MSTKMAD/MK2/03.Firmware/XX.MISC/MAIN 731/SW_EDCPSU_731.rtf

Version | Date | Author | Comment
726 | 21/6/21 | DGB | Only 2 memories instead of 4
727 | 21/6/21 | DGB | Only change memory when output is OFF (Outlatch = OFF)
Channel output changes state together with memory.
Commented the Test section of code.
All serial info is removed because is overlapped with ENA and CHANNEL.
Time of displaying ON / OFF is changed from 1800 to 800
CONT ON is changed to OUT1 ON or OUT2 ON
CONT OFF is changed to OUT OFF
Displaying the ON or OFF has changed to accommodate the indication of 1 and 2.
Libraries have been included in the project to make sure that the version is not changed.
GFX library has been modified (write function) to remove the check of the text>longer than the screen size (that makes the text to wrap).
Version of Arduino used for compilation: 1.8.13
728 | 21/6/21 | DGB | Usage of program memory is 88%
Inverted the CH1 and CH2 to allow pin to pin facing in the daughter board
Removed OVC_ALARM
ISENSE MAX Low limit is raised to be closer to the MAX (reduced hysteresis).
729 | 11 OCT 21 | DGB | Time for ISENSE MAX is changed from 1.6s to 2s
730 | 10 marzo 2022 | DGB | Removed the MEMORIES BOX from the display because it is confusing as there is only 2 possible memories.
Implemented on the main branch (725.3 and not in the DUAL so far)!!
731 | 22 marzo 2022 | DGB | NITRO is now more compatible with Cheyenne machines that have brushless motors. The NITRO is split in two phases: 1) warming phase of 65ms at 4V to awake the machine, and 2) NITRO ramp in RC charge fashion from 4 to 12.3V in around 50ms. Finally the voltage goes to encoderPos (target voltage).
