MSTKMAD/MK2/02.Hardware/MK2 PCBs/03.TESTS/PRUEBA MECANICA-EDCPSUr16D/MECH_EDCPSUr16D_USBC/EDCPSU_M2 v1.dxf

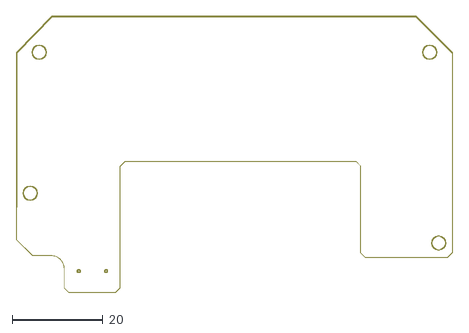
[picture p18: CAD file, 2022-08-05]
02.Hardware/MK2 PCBs/03.TESTS/PRUEBA MECANICA-EDCPSUr16D/MECH_EDCPSUr16D_USBC/EDCPSU_M2 v1.dxf
96.1 x 60.8
