MSTKMAD/MK2/02.Hardware/MK2 PCBs/03.TESTS/USBC-OVC_LIMIT/CAMOutputs/DrawingFiles/USBC-OVC_LIMIT.dxf

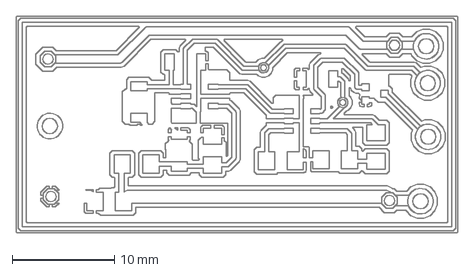
[picture p19: CAD file, 2022-08-05]
02.Hardware/MK2 PCBs/03.TESTS/USBC-OVC_LIMIT/CAMOutputs/DrawingFiles/USBC-OVC_LIMIT.dxf
43.2 x 21.2 mm
