MSTKMAD/MK2/02.Hardware/MK2 PCBs/04.FAJA USBC/FAJA_LARGA_USBC.dxf

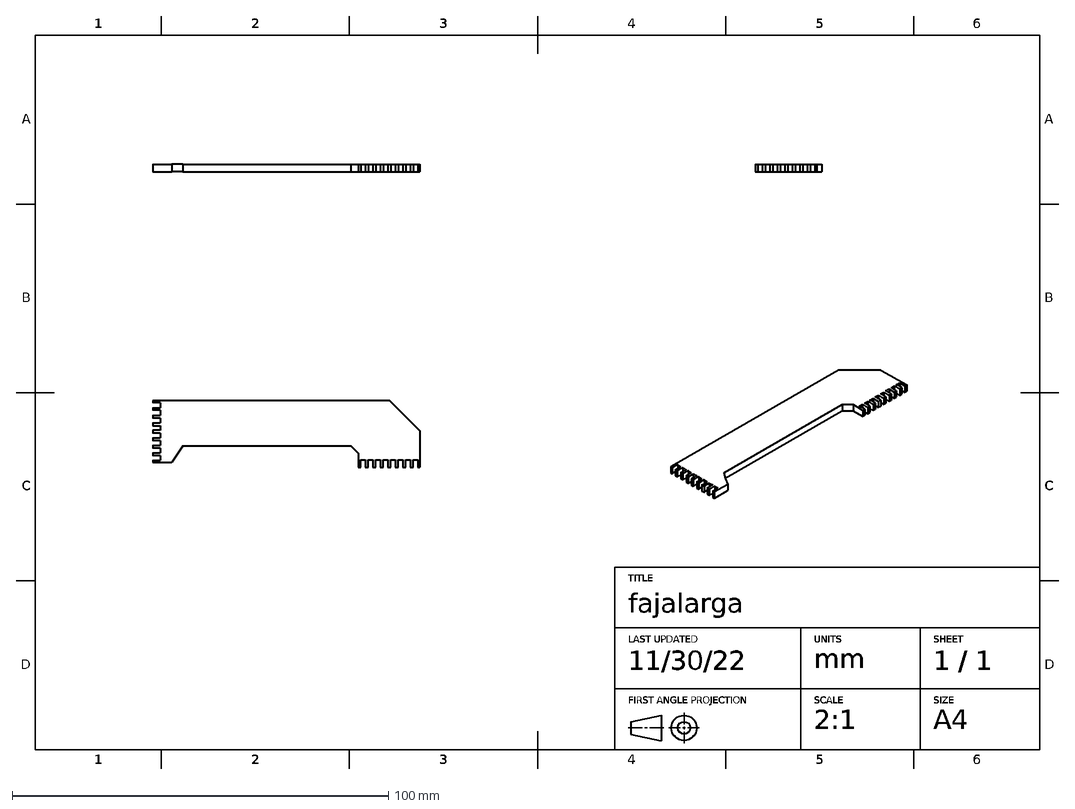
[picture p20: CAD file, 2022-11-30]
02.Hardware/MK2 PCBs/04.FAJA USBC/FAJA_LARGA_USBC.dxf
1
2
3
4
5
6
D
C
B
A
TITLE
fajalarga
LAST UPDATED
11/30/22
UNITS
mm
SHEET
1 / 1
FIRST ANGLE PROJECTION
SCALE
2:1
SIZE
A4
