MSTKMAD/MK2/02.Hardware/MK2 PCBs/02.CONNECTORS/01.Single/FRONT_USBC_1HC_v30.dxf

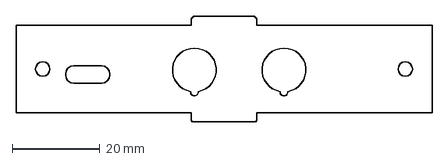
[picture p21: CAD file, 2022-06-15]
02.Hardware/MK2 PCBs/02.CONNECTORS/01.Single/FRONT_USBC_1HC_v30.dxf
95.0 x 24.0 mm
