MSTKMAD/MK2/02.Hardware/MK2 PCBs/03.TESTS/Lentilla/shapr3d_export_2022-05-11_18h31m.dxf

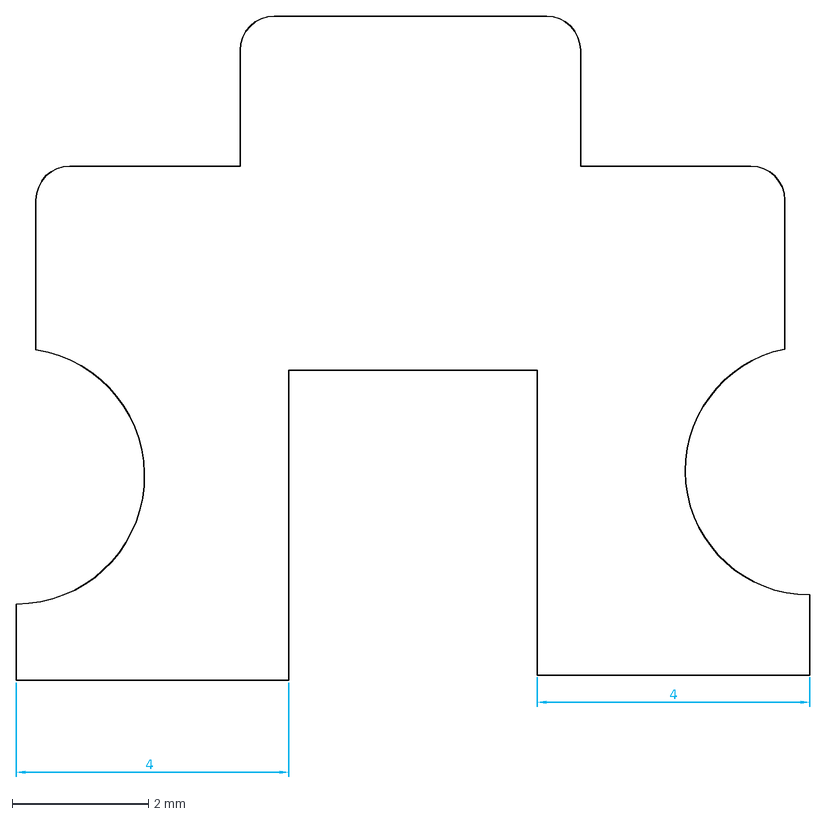
[picture p22: CAD file, 2022-08-05]
02.Hardware/MK2 PCBs/03.TESTS/Lentilla/shapr3d_export_2022-05-11_18h31m.dxf
4
