MSTKMAD/MK2/02.Hardware/MK2 PCBs/04.FAJA USBC/FAJA.dxf

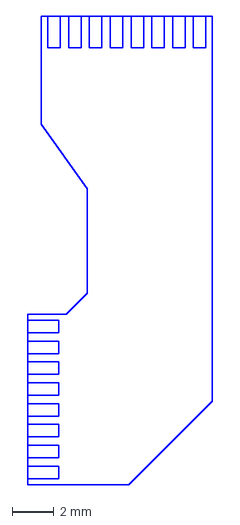
[picture p23: CAD file, 2022-06-13]
02.Hardware/MK2 PCBs/04.FAJA USBC/FAJA.dxf
8.86 x 22.5 mm
