MSTKMAD/MK2/02.Hardware/MK2 PCBs/03.TESTS/Lentilla/shapr3d_export_2022-05-11m.dxf

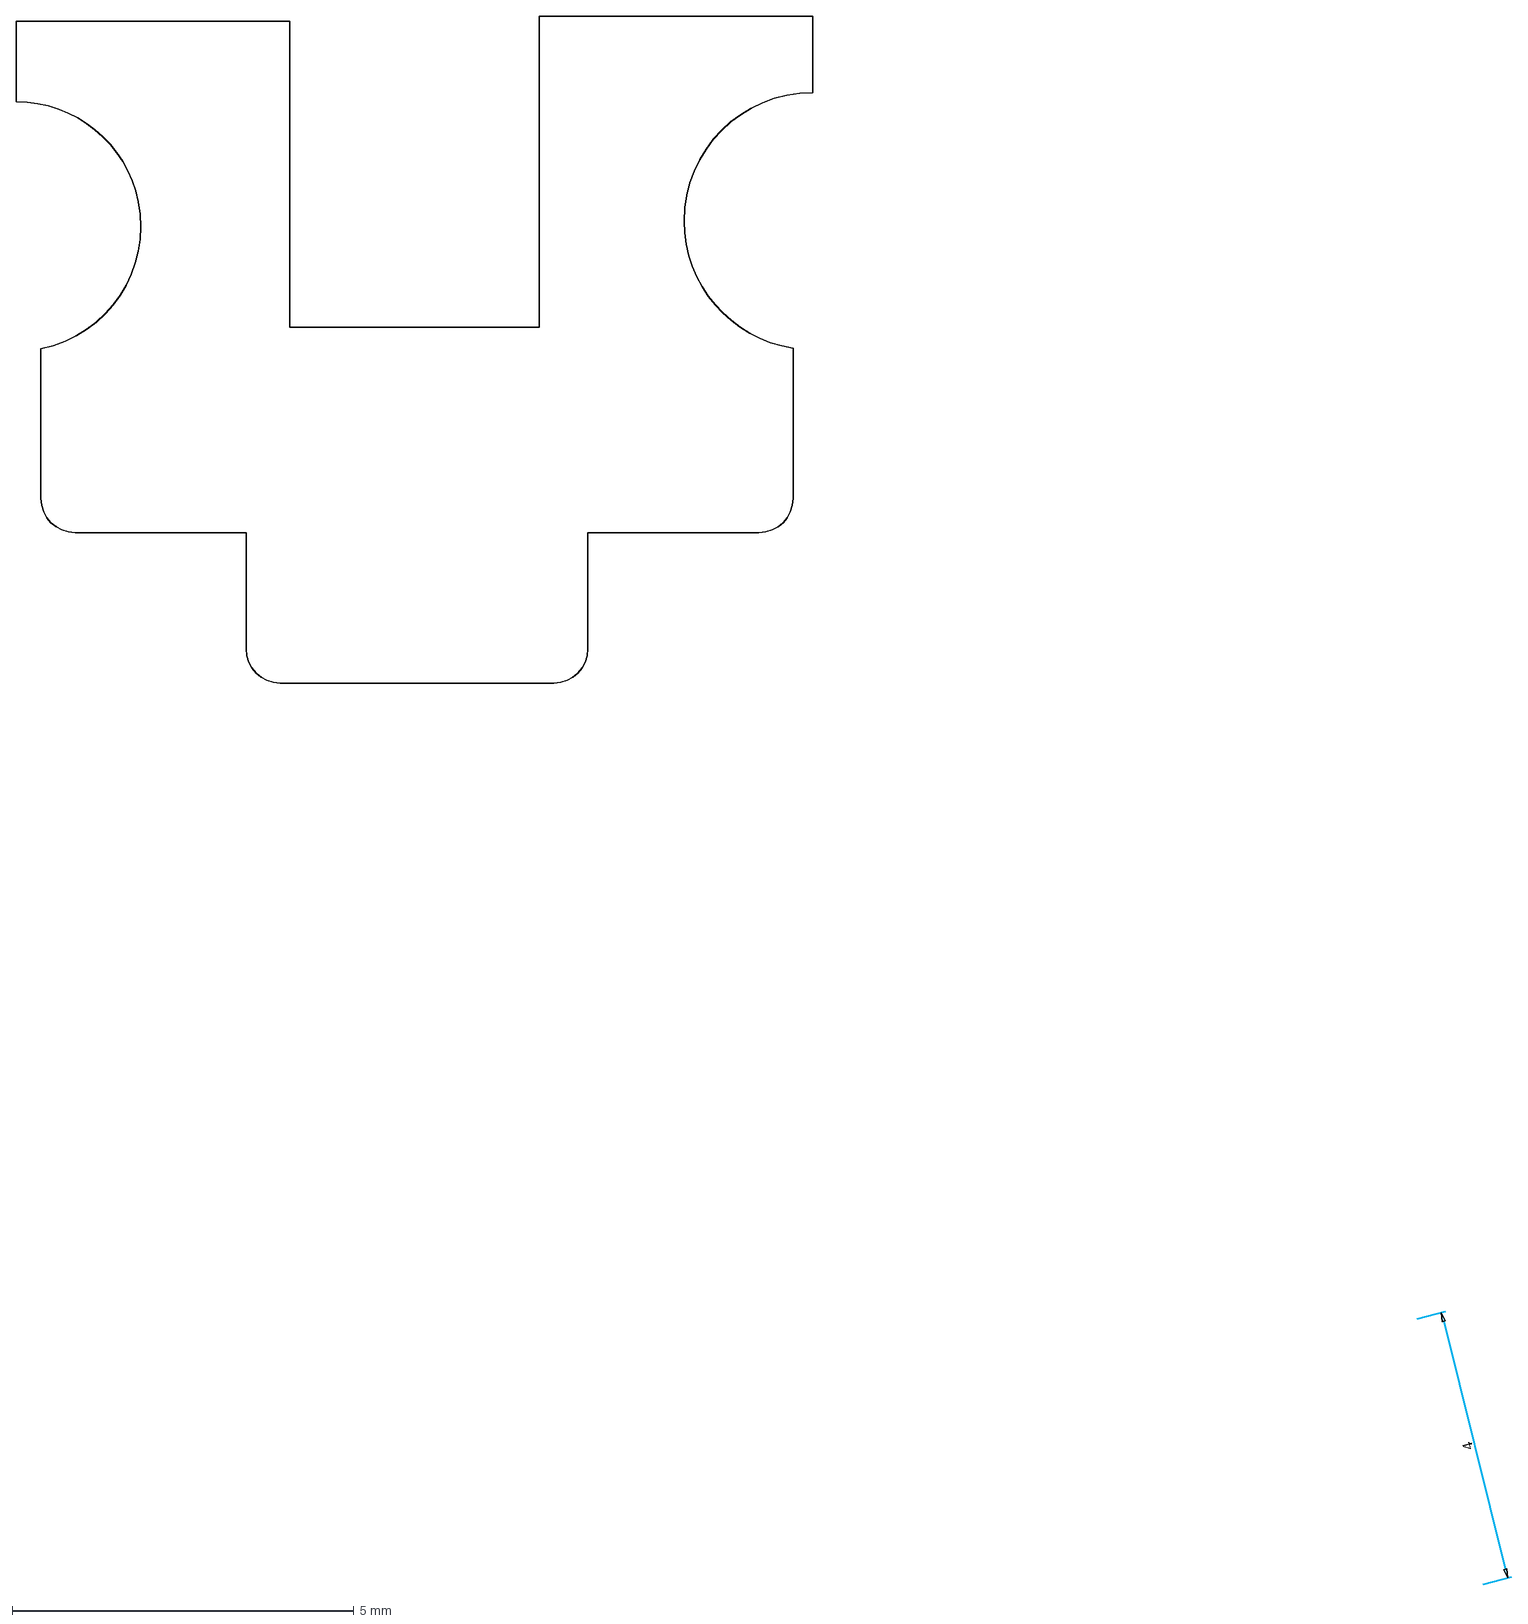
[picture p24: CAD file, 2022-08-05]
02.Hardware/MK2 PCBs/03.TESTS/Lentilla/shapr3d_export_2022-05-11m.dxf
4
