MSTKMAD/MK2/02.Hardware/MK2 PCBs/03.TESTS/PRUEBA MECANICA-EDCPSUr16D/MECH_EDCPSUr16D_USBC/EDCPSU_M2 v1.brd

## EAGLE design 02.Hardware/MK2 PCBs/03.TESTS/PRUEBA MECANICA-EDCPSUr16D/MECH_EDCPSUr16D_USBC/EDCPSU_M2 v1.brd (2022-08-05)

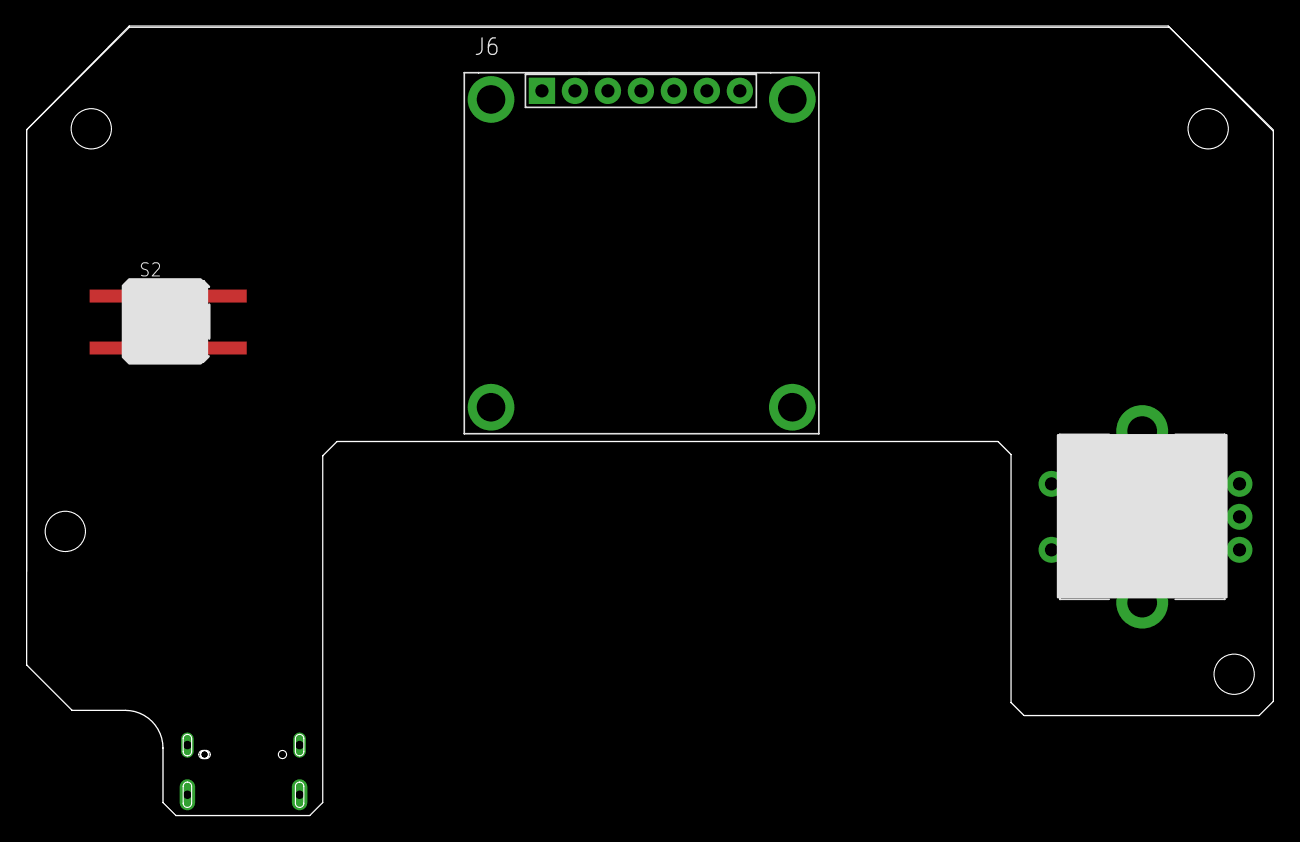
[picture p81: board EDCPSU_M2 v1.brd from above]

Board: 4 copper layers, 96.0 x 60.7 mm, 4 parts (1 on the bottom side), 2 nets, no tracks yet.

Parts:
J4: DX07S016JA1R1500; JAE_DX07S016JA1R1500
J6: Display; OLED_LCD
S1: ROTARTY_ENCODER; ROTARY_ENC_PLAIN
S2: TAC_SW_SMD_KSC931G

Connections:
GND: J4.1, J4.12
VBUS: J4.2, J4.11
