MSTKMAD/MK2/02.Hardware/MK2 PCBs/02.CONNECTORS/00.Dual/Connectors-MK2.brd

## EAGLE design 02.Hardware/MK2 PCBs/02.CONNECTORS/00.Dual/Connectors-MK2.brd (2022-05-24)

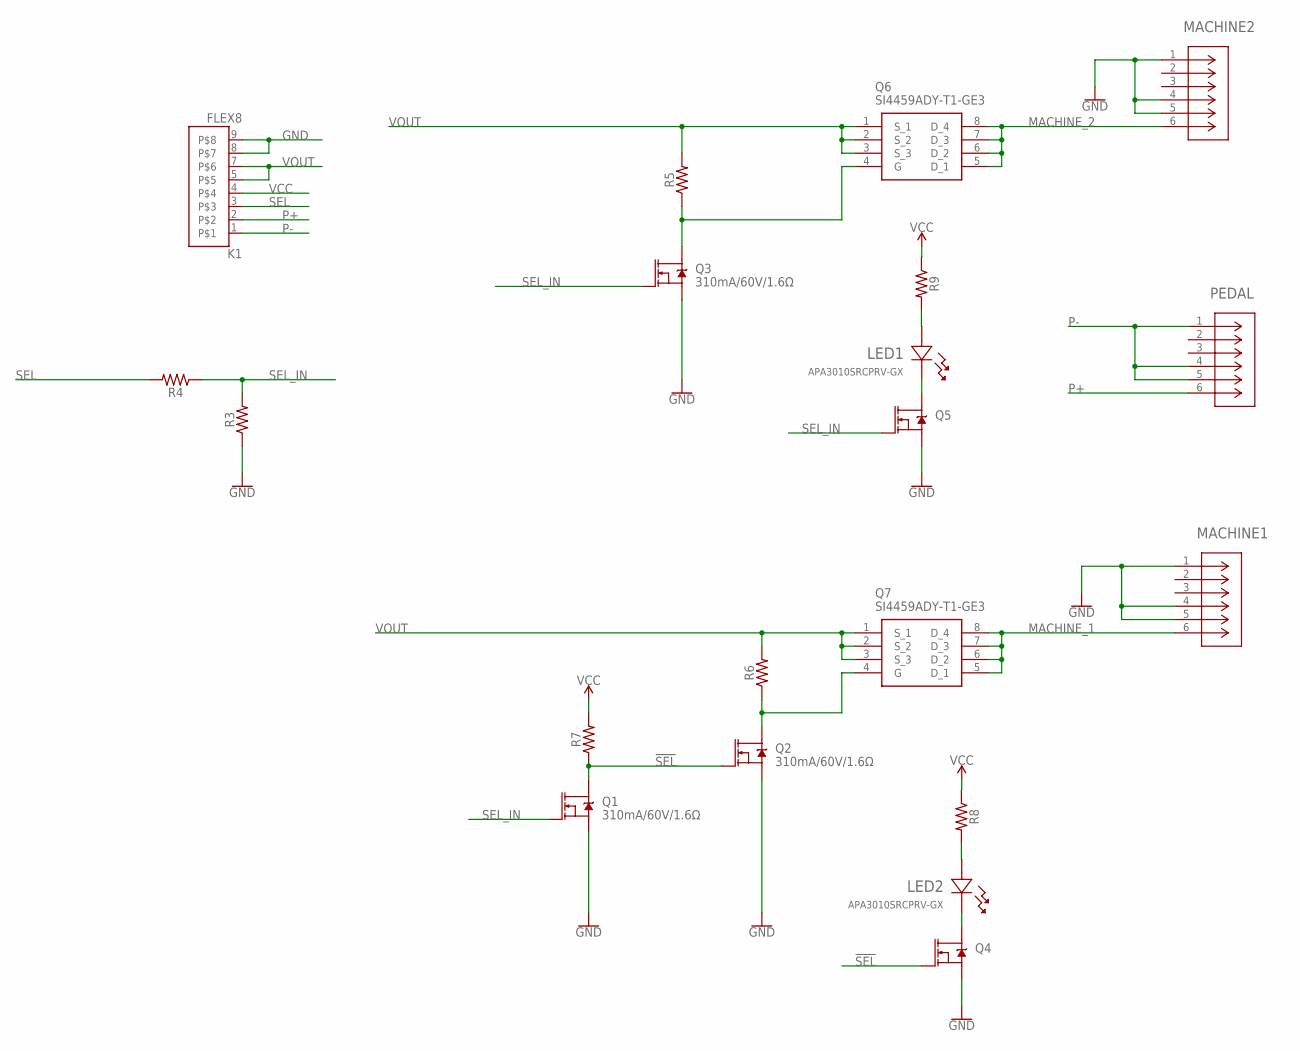
[picture p82: schematic Connectors-MK2.sch]

Parts:
K1: FLEX8
LED1, LED2: APA3010SRCPRV-GX; LED_APA3010SRCPRV-GX_KNB
MACHINE1, MACHINE2: ACJS-MHDR; CONN_MHDR_AMP
PEDAL: ACJS-MHDR; CONN_MHDR_AMP
Q1, Q2, Q3, Q4, Q5: 310mA/60V/1.6Ω; SOT323
Q6, Q7: SI4459ADY-T1-GE3; SOIC127P600X175-8N
R3, R4, R5, R6, R7: 0603
R8, R9: 0805

Connections:
!SEL!: Q1.3 (D), Q2.1 (G), Q4.1 (G), R7.1
GND: K1.8, K1.9, MACHINE1.1, MACHINE1.4, MACHINE1.5, MACHINE2.1, MACHINE2.4, MACHINE2.5, Q1.2 (S), Q2.2 (S), Q3.2 (S), Q4.2 (S), Q5.2 (S), R3.1
MACHINE_1: MACHINE1.6, Q7.5 (D_1), Q7.6 (D_2), Q7.7 (D_3), Q7.8 (D_4)
MACHINE_2: MACHINE2.6, Q6.5 (D_1), Q6.6 (D_2), Q6.7 (D_3), Q6.8 (D_4)
unnamed: Q2.3 (D), Q7.4 (G), R6.1
unnamed: Q3.3 (D), Q6.4 (G), R5.1
unnamed: LED2.2, R8.2
unnamed: LED2.1, Q4.3 (D)
unnamed: LED1.2, R9.2
unnamed: LED1.1, Q5.3 (D)
P+: K1.2, PEDAL.6
P-: K1.1, PEDAL.1, PEDAL.4, PEDAL.5
SEL: K1.3, R4.2
SEL_IN: Q1.1 (G), Q3.1 (G), Q5.1 (G), R3.2, R4.1
VCC: K1.4, R7.2, R8.1, R9.1
VOUT: K1.5, K1.7, Q6.1 (S_1), Q6.2 (S_2), Q6.3 (S_3), Q7.1 (S_1), Q7.2 (S_2), Q7.3 (S_3), R5.2, R6.2

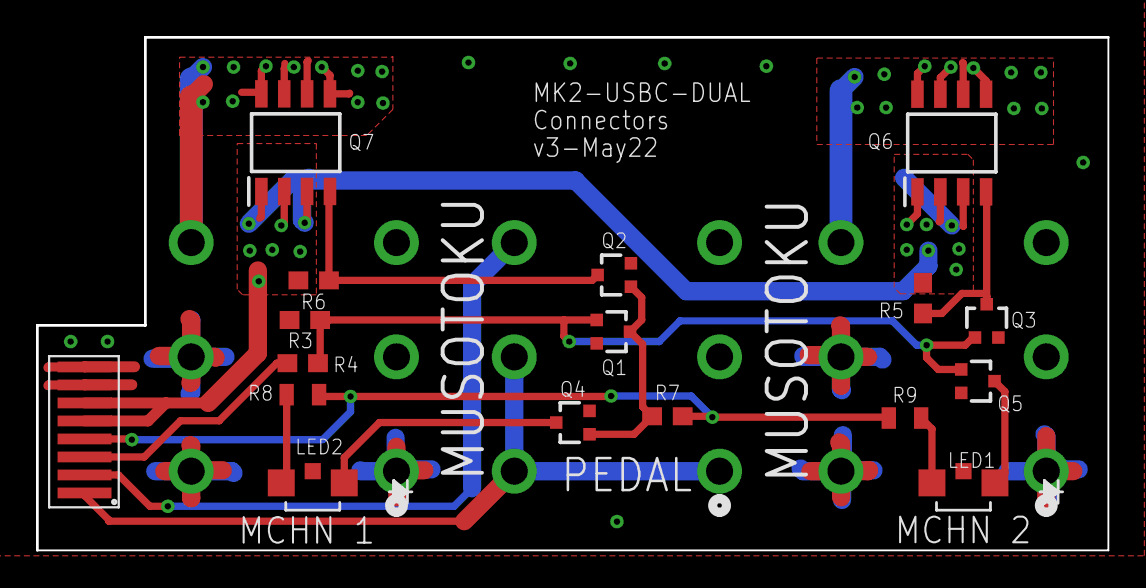
[picture p83: board Connectors-MK2.brd from above]

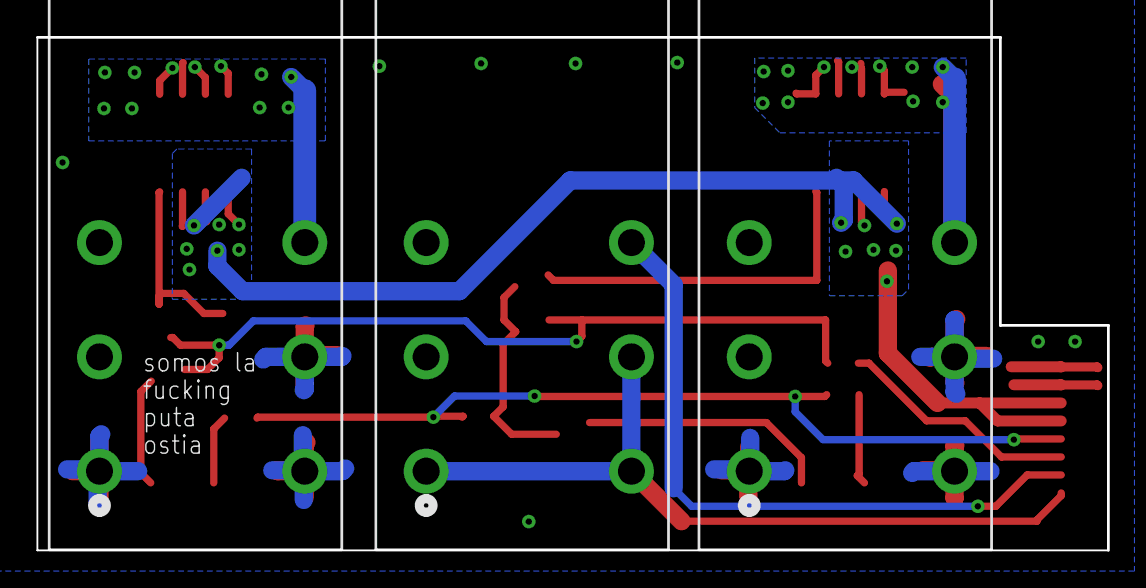
[picture p84: board Connectors-MK2.brd from below]

Board: 2 copper layers, 59.5 x 28.5 mm, 20 parts (3 on the bottom side), 16 nets.
